yossiyossy/maJIStic/docs/images/IMG_2115.jpeg

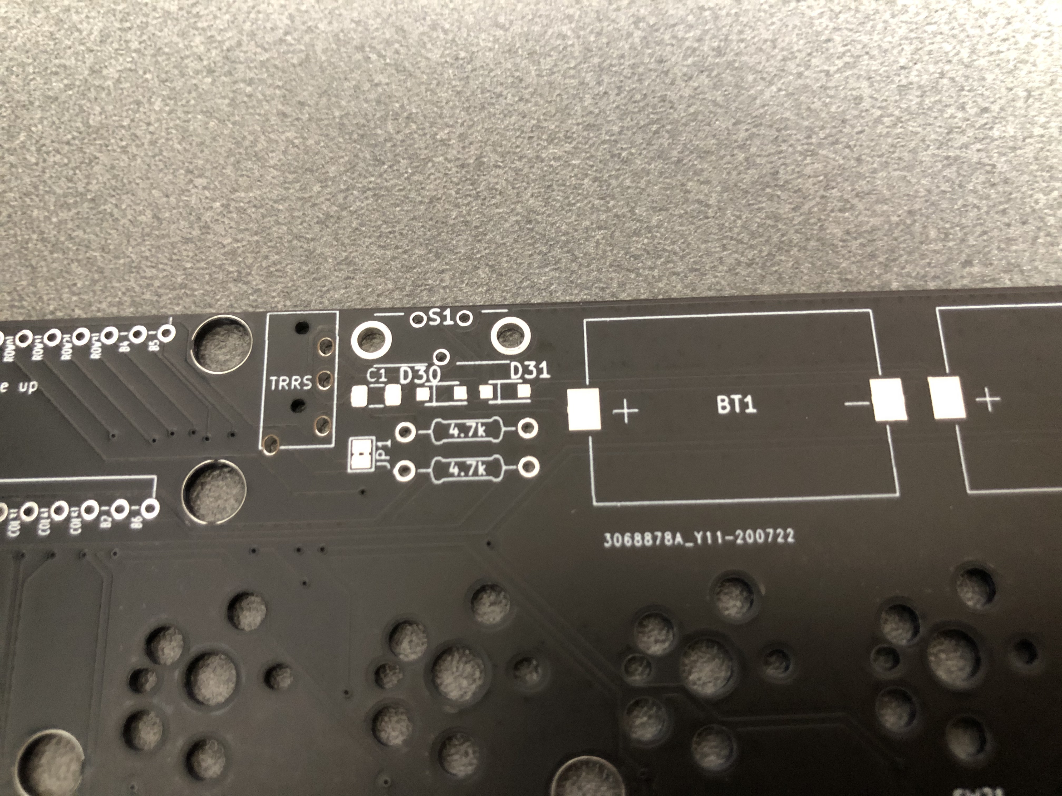
docs/images/IMG_2115.jpeg
