yossiyossy/maJIStic/docs/images/IMG_2122.jpeg

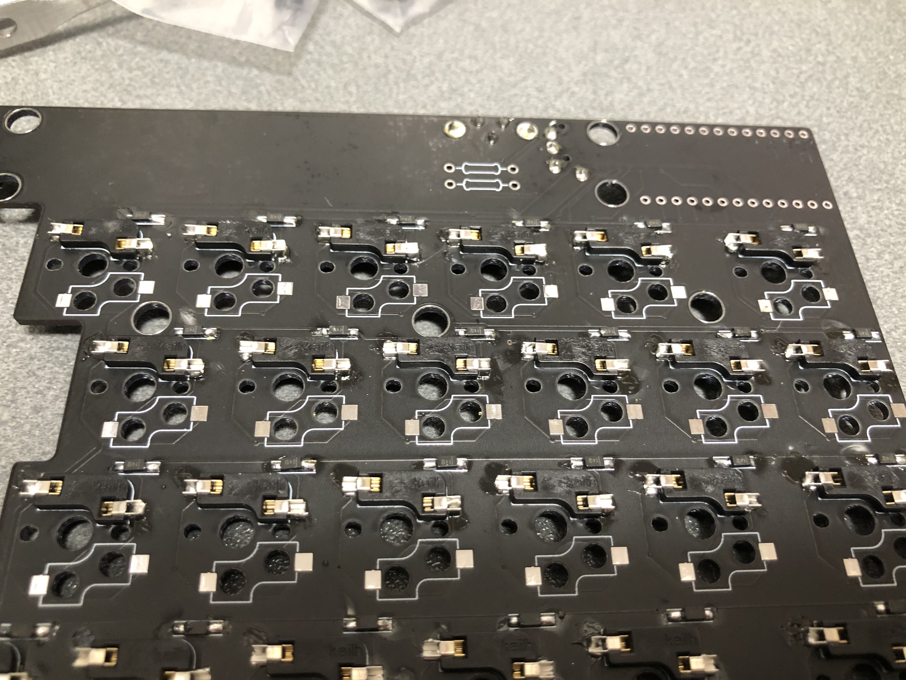
docs/images/IMG_2122.jpeg
